Sussex-Neuroscience/LL-behaviour-HF/hardware/lick_sensor/berlin_initial_model/IMG_20200210_141819.jpg

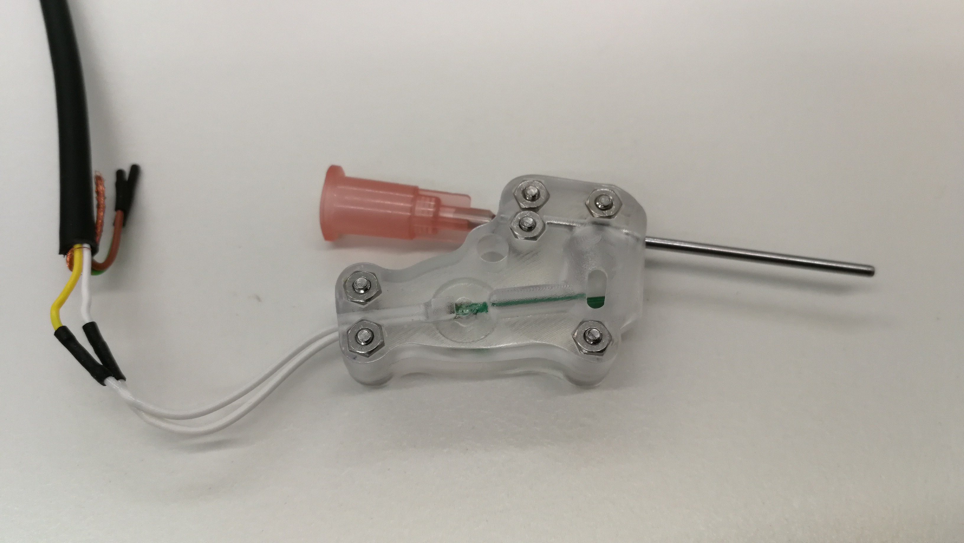
hardware/lick_sensor/berlin_initial_model/IMG_20200210_141819.jpg
