Sussex-Neuroscience/LL-behaviour-HF/software/host_computer.py

####all of this is still running on python2!!!!!

##Should figure out if it is worth to upgrade the system!!!





from __future__ import division  # important

from psychopy import visual, event, core, data, gui, monitors

import numpy, random, sys, math

from psychopy.visual.windowwarp import Warper

from datetime import datetime

import csv
#import serial



#eventually remove labjack from system

#for that we connect via serial to the ESP32

#import serial



#from U6io import U6io

#previous code was using a custom written library.

#the one below is the standard library from Labjack producers. 

#should be used instead of the custom one, as it is maintained and supported 

#by the company. and does the same as the custom one.

import u6



labjack = u6.U6()

#check wich FIOs are analog and which are digital 

#configDict = d.configIO()



timewave = []

timex = []

# --------------------------------------------Setting Up LabJack ------------------------------------------------------- #



# setup labjack U6 --> could this be made into variables or a little function for reading easiness?

# something like:

optoChannel = 0

#twoPtrigger = 1

pupilCamera = 2

#screen = 3



# then everytime the setOutputVoltageFIO is called, one could call by the names instead of numbers

labjack.setDOState(optoChannel, 0)  # channel for opto  

#labjack.setDOState(twoPtrigger, 0)  # channel for 2P trigger (on during all experiment)  

labjack.setDOState(pupilCamera, 0)  # channel for pupil camera (1 pulse per frame)  

#labjack.setDOState(screen, 0)  # channel for timewave (on when stim on)  



# labjack.setOutputVoltageFIO(0,0) # channel for opto

# labjack.setOutputVoltageFIO(1),0) # channel for 2P trigger (on during all experiment)

# labjack.setOutputVoltageFIO(2,0) # channel for pupil camera (1 pulse per frame)

# labjack.setOutputVoltageFIO(3,0) # channel for timewave (on when stim on)





# ------------------------------------------ Stimulus Parameters ------------------------------------------------------#



info = {}



info["trialN"] = 100

info["RefreshRate"] = 120  # Refresh rate of the monitor, in Hz

info["PreStim"] = info["RefreshRate"] * 2

info["StimLength"] = info["RefreshRate"] * 5 #-> is this the correct stim lenght? (originally the code was 2 seconds, but from Sina 

# description of the task it should be 5 seconds?)

info["ISI"] = info["RefreshRate"] * 2



info["Orientation"] = 315  # ,180,90,270,45,225,135,315,0 = vertical right

info["SF"] = 0.04  # cycles per degree

info["TF"] = 1  # in Hz (1 cycles per seconds = 1Hz = 1/60)

info["Contrast"] = 1

info["SD_grating"] = 3  # the "SD" of the mask 'gauss'. The default value is 3*SD

info["Position"] = [47.5106513, 2.88901593]



sizeGrating = 20



info["size"] = sizeGrating



mon = monitors.Monitor("StimMonitor")



win = visual.Window(

    fullscr=True, monitor=mon, screen=1, waitBlanking=False, useFBO=True

)  # waitBlanking=False if you want 120Hz

grating = visual.GratingStim(

    win, units="deg", mask="circle", sf=info["SF"], tex="sin", pos=info["Position"]

)  # maskParams = {'sd':3} for mask 'gauss' and maskParams = {'fringeWidth':0.2} for 'raisedCos'

grating.phase = 0.5

warper = Warper(

    win,

    warp="spherical",

    warpfile="",

    warpGridsize=128,

    eyepoint=[0.5, 0.5],

    flipHorizontal=False,

    flipVertical=False,

)



win2 = visual.Window(

    fullscr=True, monitor=mon, screen=2, waitBlanking=False, useFBO=True

)  # waitBlanking=False if you want 120Hz

grating2 = visual.GratingStim(

    win2, units="deg", mask="circle", sf=info["SF"], tex="sin", pos=info["Position"]

)  # maskParams = {'sd':3} for mask 'gauss' and maskParams = {'fringeWidth':0.2} for 'raisedCos'

grating2.phase = 0.5

warper2 = Warper(

    win2,

    warp="spherical",

    warpfile="",

    warpGridsize=128,

    eyepoint=[0.5, 0.5],

    flipHorizontal=False,

    flipVertical=False,

)



# Calculate length Experiment:



lengthPreStim = info["PreStim"] / info["RefreshRate"]

nbOfTrials = info["trialN"]

lengthStimISI = (1 * (info["StimLength"] / info["RefreshRate"])) + (

    info["ISI"] / info["RefreshRate"]

)



lengthEXP = lengthPreStim + nbOfTrials * lengthStimISI

print ("Experiment Duration = ", str(lengthEXP), "seconds")

print ("At 5 Hz: ", str(lengthEXP * 6.07), "frames")

#---------------------------------------------------------------------------------------------------------------

monitorOrder = list()

#--------------CREATE FILE -------------------------------------------------------------------------------------



#create a file that will store the monitor side as it gets updated from the ESP32

timeNow = datetime.now()

fileName = timeNow.strftime("%Y-%b-%d-%H-%M-%S")+".csv"
fid = open(fileName,"w")
fid.write('monitorSide')
fid.close()
#writer = csv.writer(fid,lineterminator='\n')
#writer.writerow(['monitor side'])

# setup a serial connection with the ESP - this will be used when LabJack is removed from the setup
#ser = serial.Serial('/dev/ttyUSB0')  # open serial port
#print(ser.name)         # check which port was really used

#add info here to make sure the connection is made
#ser.write(b'hello')     # write a string

# --------------------------------------------- Routine ------------------------------------------------------#





#labjack.setDOState(twoPtrigger, 1)



clock = core.Clock()



for frameN in range(info["PreStim"]):  # Create a prestim

    labjack.setDOState(pupilCamera, 0)

    win.flip()

    win2.flip()

    labjack.setDOState(pupilCamera, 1)

    #labjack.setDOState(screen, 0)

    timewave.append(0)

try: # try command here to make sure that if there is a keyboard interrupt, than labjack and the opened files are closed.
    side = 0
    for thisTrial in range(info["trialN"]):

        #ADD SUBROUTINE THAT WILL WAIT FOR SERIAL COMMAND FROM ESP32

        #while ser.available() == 0:

        #    print("waiting for ESP")

        #monitorSide = ser.readline()

        #print("monitor: " + str(monitorSide))

        # Random screen chosen in each trial

        ran = [[win, grating], [win2, grating2]]

        #ranchoice = random.choice(ran)





    

        #labjack.setDOState(screen, 0)

        #lock software until stim trigger comes in

        #print str(labjack.getAIN(0))

        while labjack.getAIN(0)<2.5:

            value1 = labjack.getAIN(0)

            #print str(value1)

            

            side = labjack.getAIN(1)
            #print "side input value:" +str(side)

        if side > 1.8:
            print "here"
            ranchoice = ran[0]

            monitorOrder.append(0)
            fid = open(fileName,"a")
            fid.write('\n0')
            fid.close()
            #writer.writerow("0")

        else:
            
            fid = open(fileName,"a")
            fid.write('\n1')
            fid.close()
            ranchoice = ran[1]

            monitorOrder.append(1)

            #writer.writerow("1")



        winran = ranchoice[0]

        gratingran = ranchoice[1]

        #print "test  "

        print "Trial number", thisTrial + 1    

        print "        Size is: ", sizeGrating, "degree"

    

        timex.append(clock.getTime())

        labjack.setDOState(optoChannel, 0)



        for frameN in range(info["StimLength"]):

            gratingran.setSize(sizeGrating)

            gratingran.setPhase(

                info["TF"] / info["RefreshRate"], "+")  # To get the TF in Hz, divide TF by the refresh rate       # set like this for TF fction of speed:  grating.setPhase(mouse_dX/100,'+')

            gratingran.ori = info["Orientation"]

            gratingran.setContrast(info["Contrast"])

            gratingran.draw()

            labjack.setDOState(pupilCamera, 0)

            winran.flip()

            labjack.setDOState(pupilCamera, 1)

            #labjack.setOutputVoltageFIO(screen, 1)

            timewave.append(sizeGrating)

            dummie = labjack.getAIN(0)

            if dummie < 2.5:

                #we are timing things with the ESP32, so if the ESP has finished counting the stimulus time window, 

                #than we break the for loop and end stimulation

                break



        #ser.write("d")

        labjack.setDOState(optoChannel, 0)

        timex.append(clock.getTime())



        #maybe this could be removed, since the ESP32 is doing the time counting of ISI.

        for frameN in range(info["ISI"]):  # add an ISI or post stim interval

            labjack.setDOState(pupilCamera, 0)

            winran.flip()

            labjack.setDOState(pupilCamera, 1)

            #labjack.setDOState(screen, 0)

            timewave.append(0)

    



    labjack.setDOState(pupilCamera, 0)

    labjack.setDOState(optoChannel, 0)

    #labjack.setDOState(screen, 0)



    labjack.close()

    print(monitorOrder)

    #with open("test.csv", "wb") as output:

    #    writer = csv.writer(output, lineterminator='\n')

    #    for val in monitorOrder:
    #        writer.writerow([val]) 



except KeyboardInterrupt:#catch if there is a ctrl-c event

    labjack.close()
    #with open("test.csv", "wb") as output:
    #    writer = csv.writer(output, lineterminator='\n')#

        #for val in monitorOrder:

        #    writer.writerow([val])  





    #close serial connection with ESP

    #ser.close()             # close port
