Sussex-Neuroscience/LL-behaviour-HF/software/main.py

#import tasks
#from tests import Tests
#import tasks

#run1  = tasks.task1()
#run1.numberOfTrials = 5
#run1.run_task()
#class Main:
#    def __init__(self):
#        #self.test = Tests()
#        run1  = tasks.task1()
#        run1.numberOfTrials = 5
#        run1.run_task()
